Jimmy-Chu-127/Inflatable-Buoy-Dropper/3D printing STL files/5.12/servo connector 3.STL

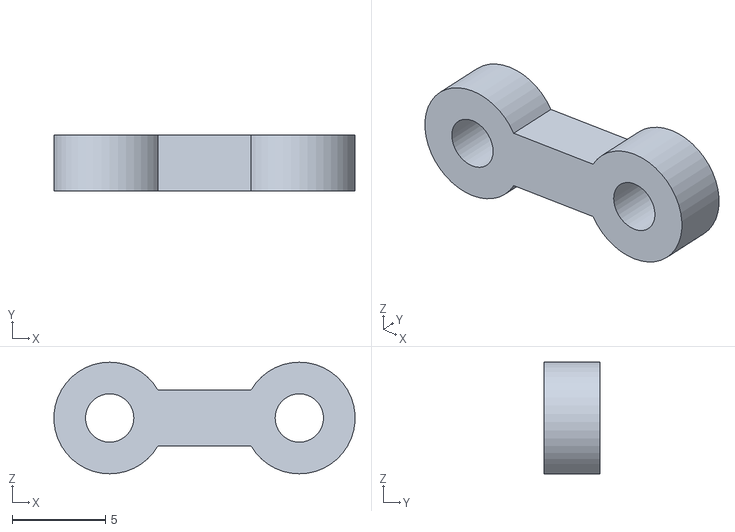
[picture p16: CAD file, 2023-05-13]
3D printing STL files/5.12/servo connector 3.STL
16.2 x 3.00 x 6.00
