Jimmy-Chu-127/Inflatable-Buoy-Dropper/3D printing STL files/servo height pad.STL

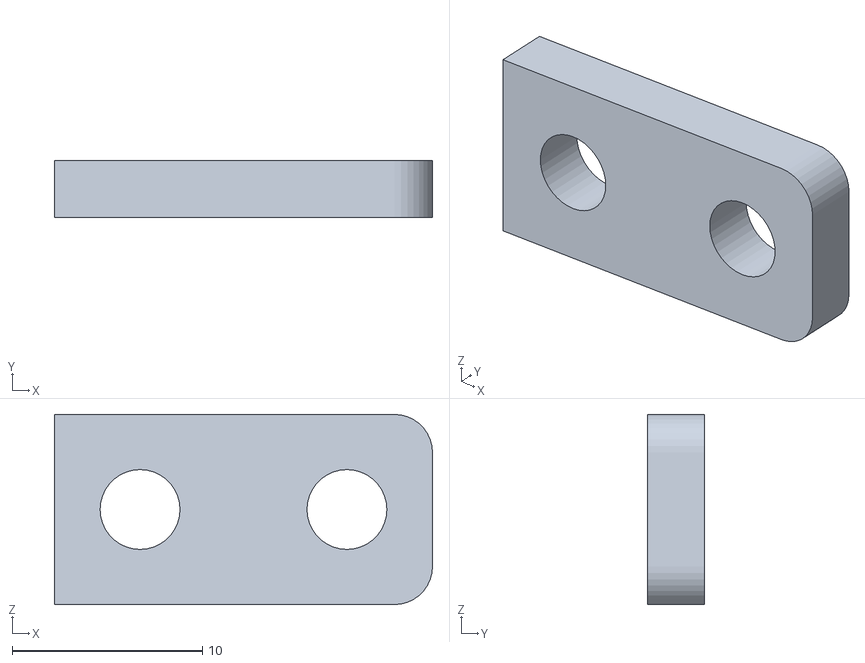
[picture p17: CAD file, 2023-06-04]
3D printing STL files/servo height pad.STL
19.9 x 3.00 x 10.0
