Jimmy-Chu-127/Inflatable-Buoy-Dropper/3D printing STL files/5.12/servo attachment.STL

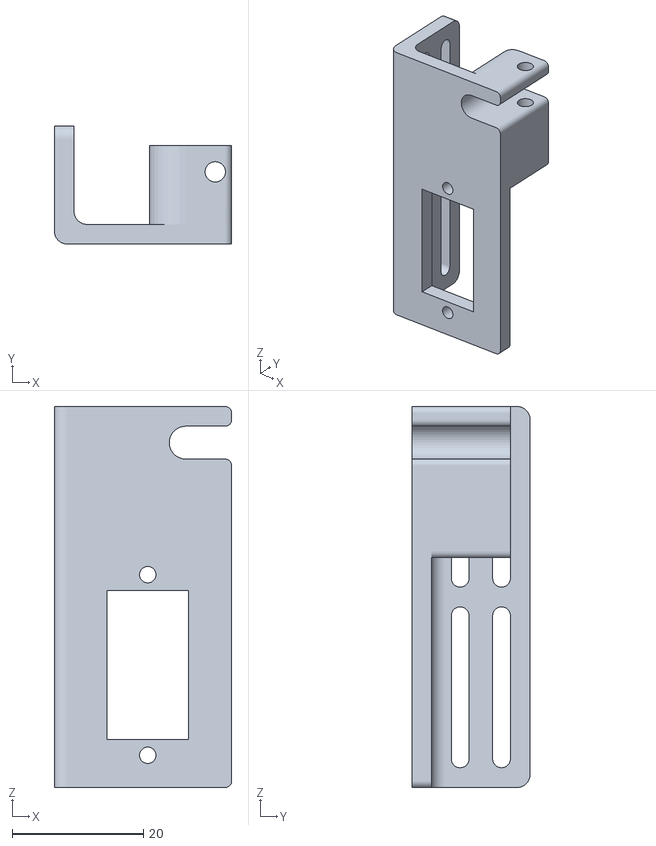
[picture p18: CAD file, 2023-05-13]
3D printing STL files/5.12/servo attachment.STL
27.0 x 18.0 x 58.0
