Jimmy-Chu-127/Inflatable-Buoy-Dropper/Assembly & Parts/servo arm.SLDPRT

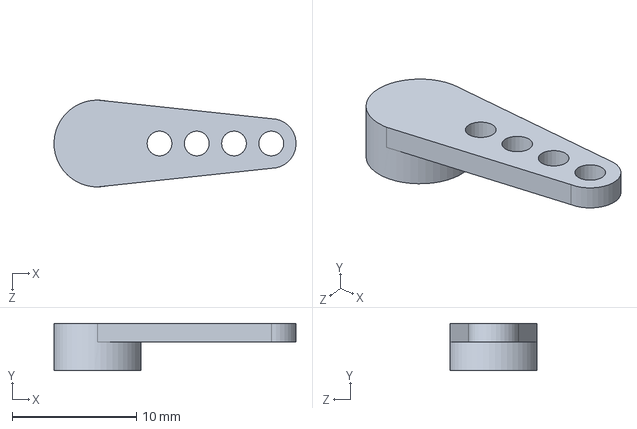
[picture p19: CAD file, 2023-05-25]
Assembly & Parts/servo arm.SLDPRT
19.5 x 3.80 x 7.00 mm
