Jimmy-Chu-127/Inflatable-Buoy-Dropper/Assembly & Parts/PCB Enclosure water insert.SLDPRT

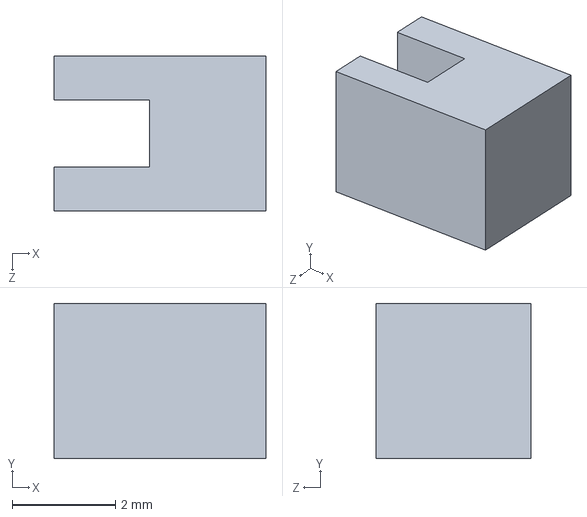
[picture p20: CAD file, 2023-05-25]
Assembly & Parts/PCB Enclosure water insert.SLDPRT
4.10 x 3.00 x 3.00 mm
