Jimmy-Chu-127/Inflatable-Buoy-Dropper/Assembly & Parts/servo.SLDPRT

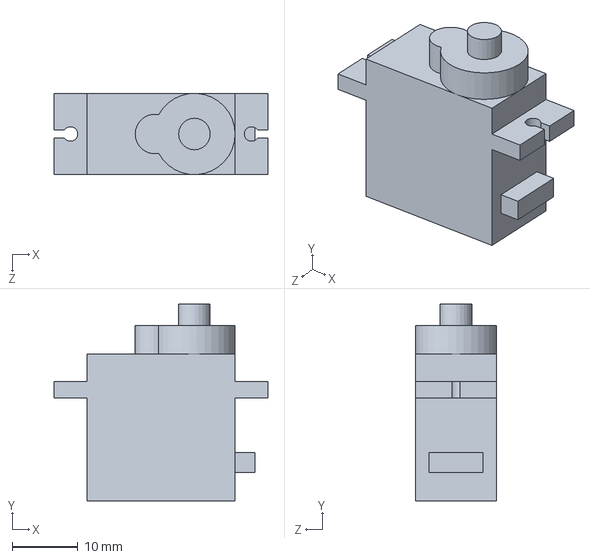
[picture p21: CAD file, 2023-05-25]
Assembly & Parts/servo.SLDPRT
32.5 x 29.9 x 12.4 mm
