Jimmy-Chu-127/Inflatable-Buoy-Dropper/Assembly & Parts/buoy holder.SLDPRT

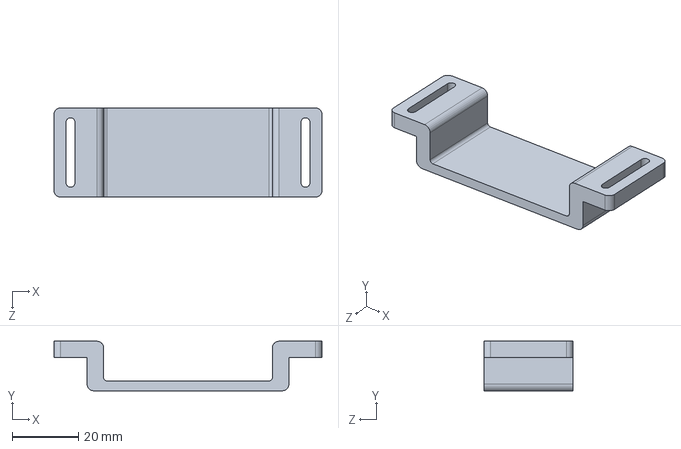
[picture p22: CAD file, 2023-05-21]
Assembly & Parts/buoy holder.SLDPRT
81.0 x 15.0 x 27.0 mm
