Jimmy-Chu-127/Inflatable-Buoy-Dropper/Assembly & Parts/bottom attachment board.SLDPRT

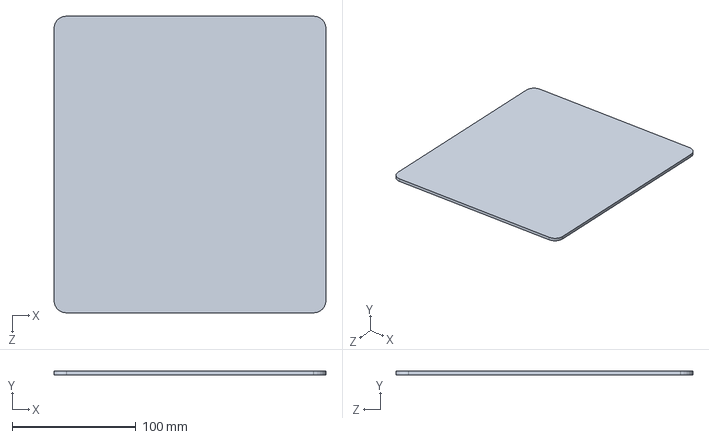
[picture p23: CAD file, 2023-05-21]
Assembly & Parts/bottom attachment board.SLDPRT
220.0 x 3.17 x 240.0 mm
