Jimmy-Chu-127/Inflatable-Buoy-Dropper/Assembly & Parts/servo connector.SLDPRT

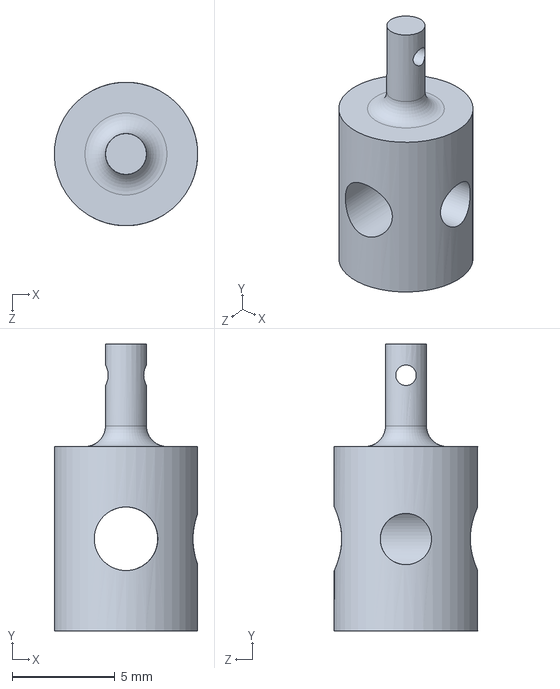
[picture p24: CAD file, 2023-05-04]
Assembly & Parts/servo connector.SLDPRT
7.00 x 14.0 x 7.00 mm
